prydin/param-eq/ui/src/registers.cpp

#include "registers.h"
#include "netconv.h"

namespace {
void unpackFftWord(uint32_t word, uint8_t *dst, uint8_t wordIndex) {
    const size_t base = static_cast<size_t>(wordIndex) * 4U;
    if (base + 3U >= 16U) {
        return;
    }

    // DSP packs groups as b0 in LSB through b3 in MSB before byte-order conversion.
    dst[base + 0U] = static_cast<uint8_t>(word & 0xFFU);
    dst[base + 1U] = static_cast<uint8_t>((word >> 8) & 0xFFU);
    dst[base + 2U] = static_cast<uint8_t>((word >> 16) & 0xFFU);
    dst[base + 3U] = static_cast<uint8_t>((word >> 24) & 0xFFU);
}

void accumulateFftWordMax(uint32_t word, volatile uint8_t *dst, uint8_t wordIndex) {
    const size_t base = static_cast<size_t>(wordIndex) * 4U;
    if (base + 3U >= 16U) {
        return;
    }

    const uint8_t b0 = static_cast<uint8_t>(word & 0xFFU);
    const uint8_t b1 = static_cast<uint8_t>((word >> 8) & 0xFFU);
    const uint8_t b2 = static_cast<uint8_t>((word >> 16) & 0xFFU);
    const uint8_t b3 = static_cast<uint8_t>((word >> 24) & 0xFFU);

    if (b0 > dst[base + 0U]) dst[base + 0U] = b0;
    if (b1 > dst[base + 1U]) dst[base + 1U] = b1;
    if (b2 > dst[base + 2U]) dst[base + 2U] = b2;
    if (b3 > dst[base + 3U]) dst[base + 3U] = b3;
}
} // namespace

void RegisterBank::updateRegister(uint8_t reg, uint32_t value) {
    RegisterState& w = buffers[writeBufferIndex];

    switch (reg) {
        case REG_OUT_GAIN:
            w.outputGain = ntohf(value);
            break;
        case REG_IN_GAIN:
            w.inputGain = ntohf(value);
            break;
        case REG_FILTER_SELECT:
            w.filterSelect = max(uint8_t(0), min(uint8_t(ntohl(value)), uint8_t(FILTER_BANDS - 1)));
            break;
        case REG_FILTER_FREQ:
            w.frequency = ntohf(value);
            break;
        case REG_VU_METER:
        {
            const uint32_t packed = ntohl(value);
            const uint16_t left = static_cast<uint16_t>(packed >> 16);
            const uint16_t right = static_cast<uint16_t>(packed & 0xFFFFU);

            noInterrupts();
            vuMeterPacked = packed;
            if (left > vuMeterAccumLeft) {
                vuMeterAccumLeft = left;
            }
            if (right > vuMeterAccumRight) {
                vuMeterAccumRight = right;
            }
            vuMeterDirty = true;
            interrupts();
            break;
        }
        case REG_FILTER_Q:
            w.q = ntohf(value);
            break;
        case REG_FILTER_GAIN:
            w.filterGain = ntohf(value);
            break;
        case REG_SAMPLE_RATE:
            w.sampleRate = ntohl(value);
            break;
        case REG_RESET:
            w.reset = ntohl(value);
            break;
        case REG_FILTER_TYPE:
            w.filterType = ntohl(value);
            break;
        case REG_USER_INPUT:
            w.userInput = ntohl(value);
            break;
        case REG_FILTER_COEFF0:
        case REG_FILTER_COEFF1:
        case REG_FILTER_COEFF2:
        case REG_FILTER_COEFF3:
        case REG_FILTER_COEFF4:
            w.filterCoeff[w.filterSelect][reg - REG_FILTER_COEFF0] = ntohf(value);
            break;
        case REG_FFT_DATA_L0:
        case REG_FFT_DATA_L1:    
        case REG_FFT_DATA_L2:
        case REG_FFT_DATA_L3:
        {
            const uint8_t wordIndex = reg - REG_FFT_DATA_L0;
            const uint32_t unpackedWord = ntohl(value);

            unpackFftWord(unpackedWord, w.fftLeft, wordIndex);

            noInterrupts();
            accumulateFftWordMax(unpackedWord, fftAccumLeft, wordIndex);
            fftDirty = true;
            interrupts();
            break;
        }
        case REG_DISPLAY_MODE:
            w.displayMode = ntohl(value);
            break;
        case REG_UI_MODE:
            w.uiMode = ntohl(value);
            break;
        case REG_COMMIT:
            noInterrupts();
            {
                const uint8_t oldRead = readBufferIndex;
                readBufferIndex = writeBufferIndex;
                writeBufferIndex = oldRead;

                // Keep next write buffer in sync so partial updates work as expected
                buffers[writeBufferIndex] = buffers[readBufferIndex];
                ready = true;
            }
            interrupts();
            break;
        default:
            // Handle invalid register
            break;
    }
}
